Andreea21Radu/InkTime/Images/baterie.png

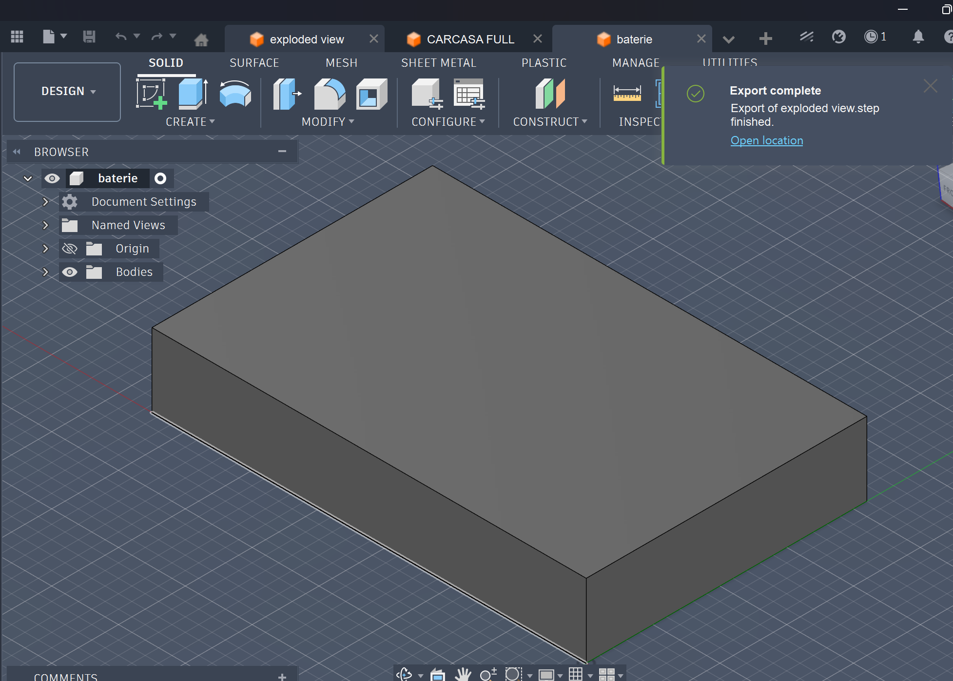
Images/baterie.png
